vmykhalchuk/RetroProgrammer/temp/20150525_211632.jpg

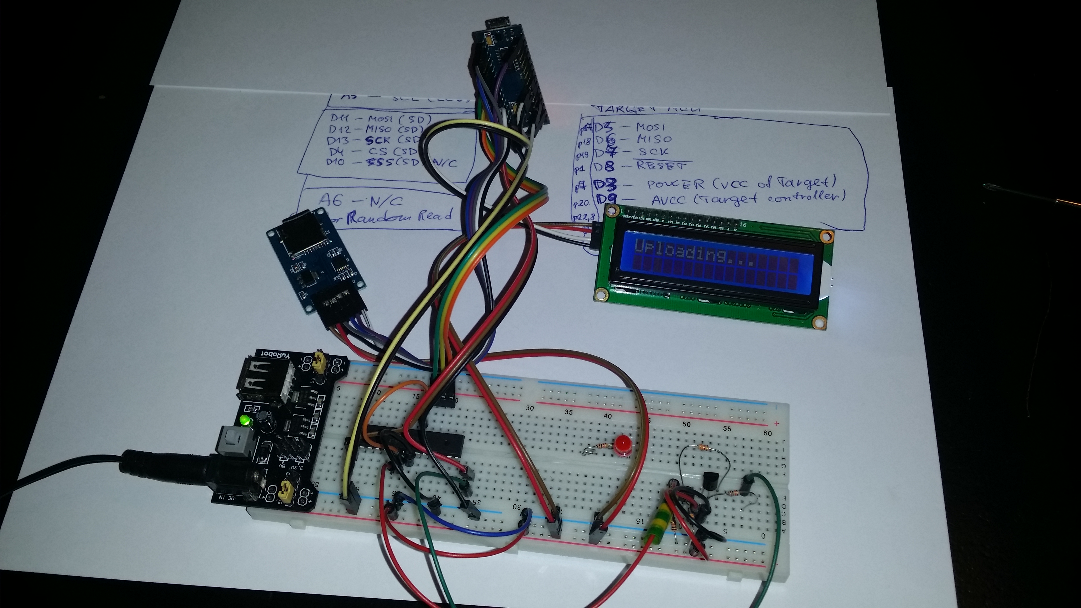
temp/20150525_211632.jpg
