vmykhalchuk/RetroProgrammer/temp/20150525_213424.jpg

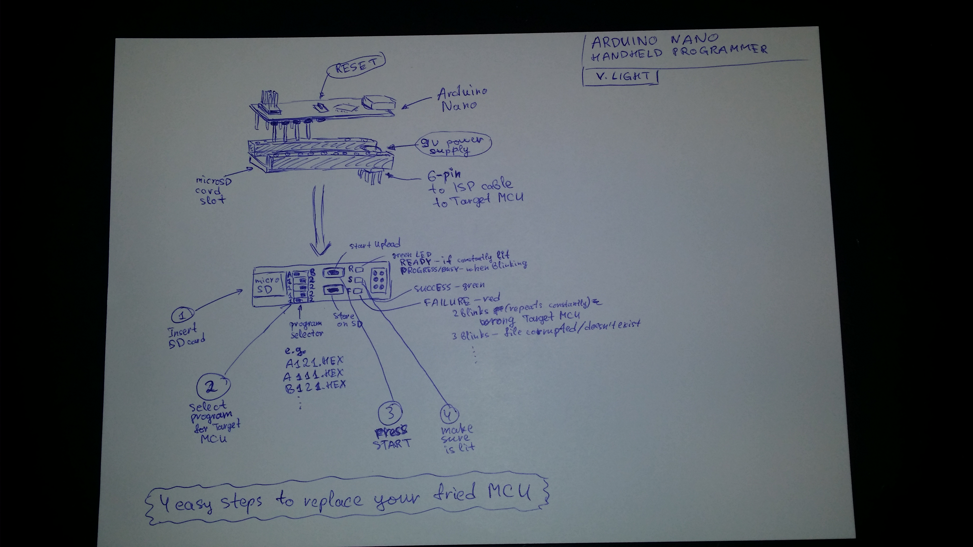
temp/20150525_213424.jpg
