vmykhalchuk/RetroProgrammer/temp/Components/Screen Shot 2015-06-24 at 10.29.37.png

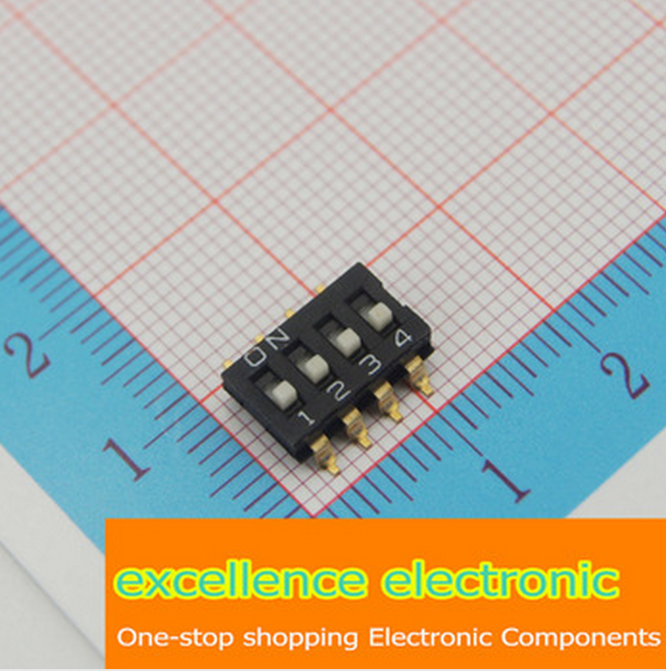
temp/Components/Screen Shot 2015-06-24 at 10.29.37.png
