vmykhalchuk/RetroProgrammer/src/RetroProgrammer/Tests.h

#ifndef Tests_h
#define Tests_h

  #include <Arduino.h>
  #include "Statuses.h"
  #include "LoggerA.h"
  #include "Utils.h"
  #include "AVRConstants.h"
  #include "AVRProgrammer.h"
  #include "TargetProgramDetector.h"
  #include "ConfFile.h"
  #include "HEXFile.h"
  #include "ProgramFile.h"
  #include "HWInterface.h"

  /**
   * Test ports on Board
   */
  class Tests_Board {
    public:
    // !!! call only one method at once
    static void testManualProgramSelectorPorts();
    static void testSDCardPorts();
  };

  /*
   * Requires Target MCU connected
   */
  class Tests_AVRProgrammer {
    public:
    static void testAVRSignatureRead();
    // Carefull with this method, it will upload page to MCU!
    static void testUploadProgramTestPage(int targetMcuModelId, int pageNo, byte* pageToUpload, int pageSize);
  };

  /**
   * 1) requires SD Card to be connected (see ConfFile.h for more details)
   * 2) requires test files to be written to SD card
   */
  class Tests_ConfFile {
    public:
      static void testConfFile();
      
    private:
      static char __testConfFileName[];
      static boolean _testOpenConfFile(byte pos);
      static void testAutogenerateDirNamesByProgId();
      static void testSkipToValidData();
      static void testReadRootConfFile();
      // doesn't support strings longer then 125 characters!
      //static boolean _testStringMatches(const char* str1, const char* str2, boolean debugMode);
  };

  /**
   * Same requirements as for Tests_ConfFile
   */
  class Tests_HEXFile {
    public:
      static void testHEXFile05();
  };

  /**
   * 1) Make sure that HWInterface::setup is called; and
   * 2) proper components are attached to MCU pins
   *      a) ports: D2, A4, A5 - see schematics
   */
  class Tests_HWInterface {
    public:
      static void testLedsAndBtns();
  };

  /**
   * requires A0,A1,A2,A3 and A4 connections, depending on type of test, see schematics
   */
  class Tests_TargetProgramDetector {
    public:
    static void testTargetProgramDetector();
    static void __testOneWireID(int d);
    static void __testGetProgId(int d);
  };

  // nothing is required to run these tests (no special connections just Arduino Nano/Micro)
  void testUtilsGen();
  void __testConvertByteToHexChar();
  void __testConvertHexCharToByte();
  void __testConvertTwoHexCharsToByte();
  void __testConvert3DigitsToInt();
  void __testIsWhiteChar();
  void __testIsValidNameChar();
  void __testStrLength();

  // nothing is required to run these tests (no special connections just Arduino Nano/Micro)
  void testUtilsAVR();
  void __testGetAVRModelIdBySignature();
  void __testGetAVRModelAndConf();
  void __testGetAVRModelNameById();
  void __testGetAVRModelIdByName();

  void someOldTests();

#endif
